jankae/moonlamp/images/IMG_1853.jpg

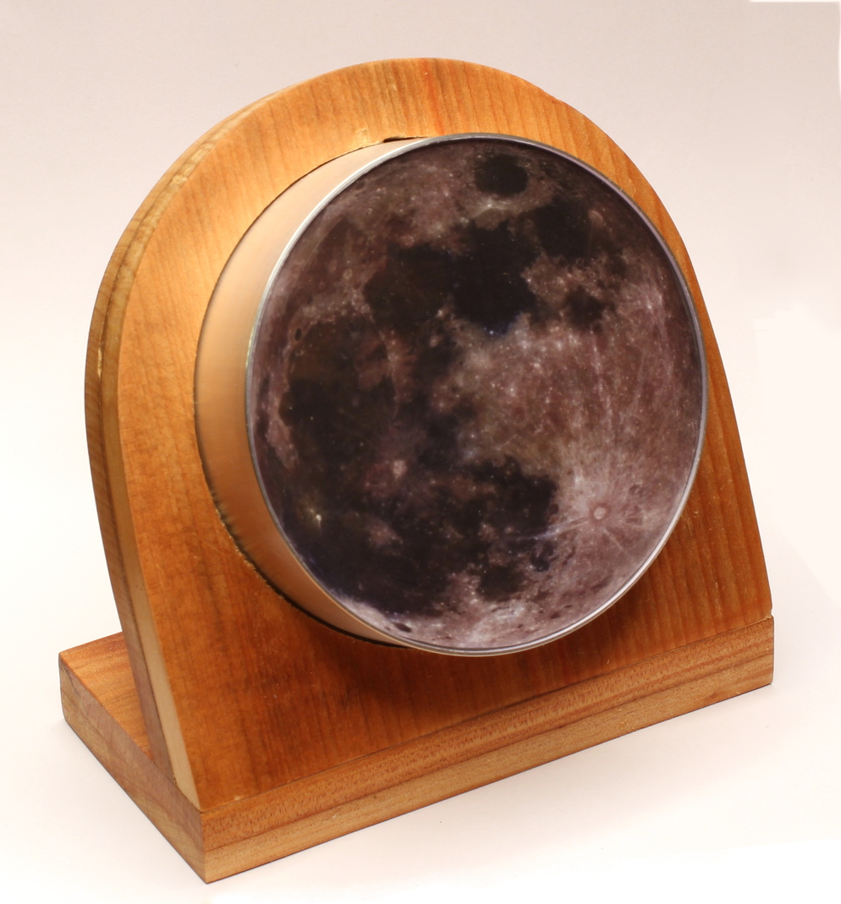
images/IMG_1853.jpg
