jankae/moonlamp/images/IMG_1859.jpg

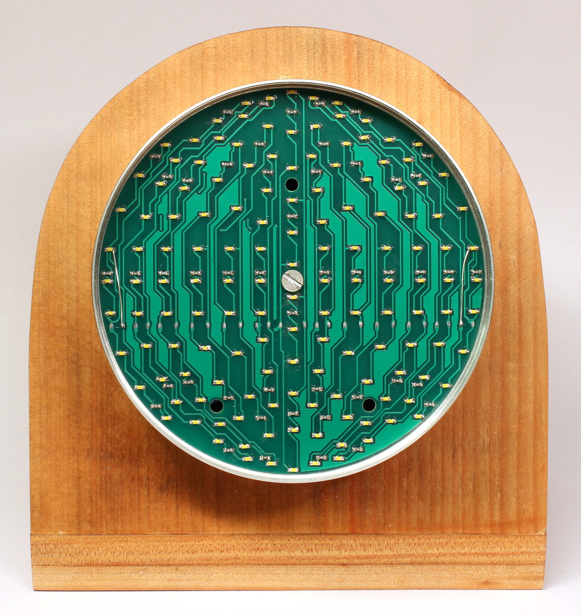
images/IMG_1859.jpg
