jankae/moonlamp/images/IMG_1860.jpg

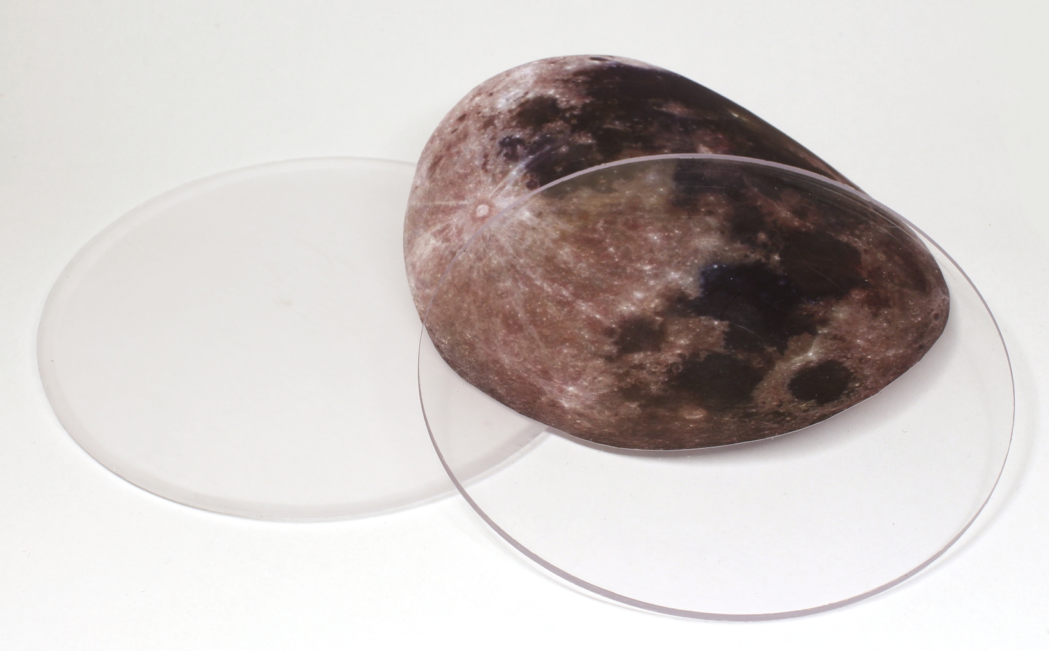
images/IMG_1860.jpg
