jankae/moonlamp/images/IMG_1861.jpg

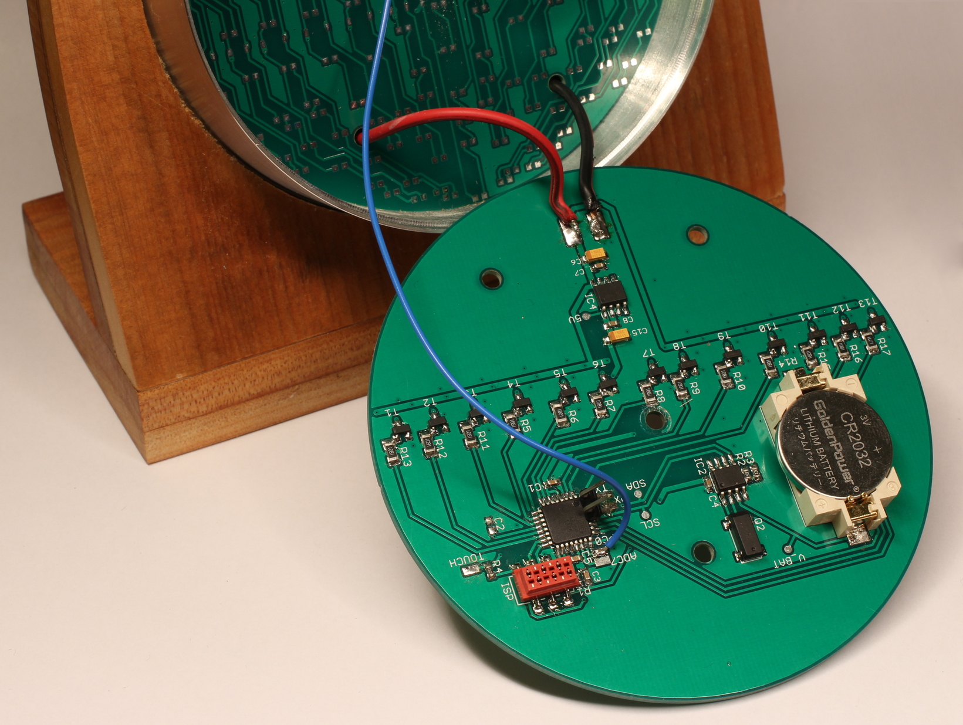
images/IMG_1861.jpg
